geaz/muRLi/circuit/kicad/MOD.sch

## KiCad design circuit/kicad/MOD.sch (2020-06-06)

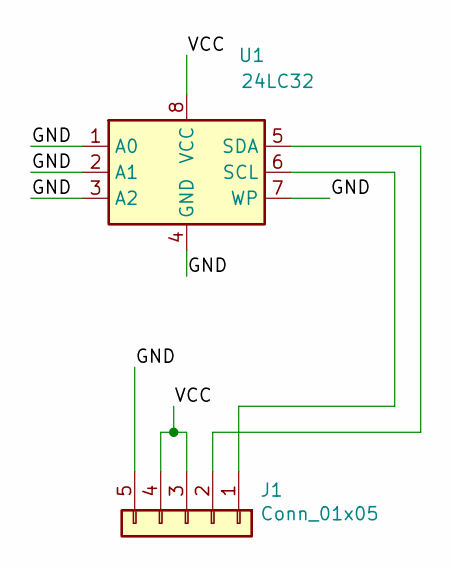
[picture p32: schematic MOD.sch]

Parts:
J1: Conn_01x05
U1: 24LC32

Connections:
GND: J1.5, U1.1 (A0), U1.2 (A1), U1.3 (A2), U1.4 (GND), U1.7 (WP)
unnamed: J1.1, U1.6 (SCL)
unnamed: J1.2, U1.5 (SDA)
VCC: J1.3, J1.4, U1.8 (VCC)
