geaz/muRLi/src/firmware/src/murli/states/invalid_mod_state.cpp

#ifndef INVALIDMODSTATE_H
#define INVALIDMODSTATE_H

#include "../state.hpp"
#include "../murli_context.hpp"
#include "../../views/icon_text_view.cpp"

namespace Murli
{
    class InvalidModState : public State
    {
        public:
            InvalidModState()
            {
                _invalidModView = std::make_shared<IconTextView>("Invalid MOD ...", u8g2_font_open_iconic_check_2x_t, 66);
            }

            void run(MurliContext& context)
            {
                context.getLed().setAllLeds(Murli::Red);
                context.getDisplay().setView(_invalidModView);
            }

        private:
            std::shared_ptr<IconTextView> _invalidModView;
    };
}

#endif // INVALIDMODSTATE_H
