geaz/muRLi/src/firmware/src/network/websocket/socket_server.cpp

#include "socket_server.hpp"

namespace Murli
{
    SocketServer::SocketServer()
    {
        _webSocket.begin();
        _webSocket.onEvent([this](uint8_t num, WStype_t type, uint8_t * payload, size_t length){ serverEvent(num, type, payload, length); });
    }

    void SocketServer::loop()
    {
        _webSocket.loop();
    }

    void SocketServer::broadcast(Client::Command command)
    {
        // Only MESH_COUNT_REQUEST and MESH_UPDATE are awaiting answers
        if (command.commandType == Client::MESH_COUNT_REQUEST
        || command.commandType == Client::MESH_UPDATE)
        {
            _answers = 0;
            _requestCommand = command;
        }

        size_t commandSize = sizeof(command);
        uint8_t serializedCommand[commandSize];
        memcpy(&serializedCommand, &command, commandSize);

        _webSocket.broadcastBIN(&serializedCommand[0], commandSize);
    }

    void SocketServer::broadcastMod(std::string& mod)
    {
        _answers = 0;
        _modDistribution = true;
        _webSocket.broadcastTXT(mod.c_str(), mod.length());
    }

    uint32_t SocketServer::getClientsCount()
    {
        return _webSocket.connectedClients();
    }

    void SocketServer::serverEvent(uint8_t num, WStype_t type, uint8_t * payload, size_t length)
    {
        IPAddress remoteIp = _webSocket.remoteIP(num);
        switch(type) 
        {
            case WStype_DISCONNECTED:              
                Serial.println("Client disconnected!");
                for(auto event : meshConnectionEvents.getEventHandlers()) event.second();
                break;
            case WStype_CONNECTED:        
                Serial.println("Connection from: " + remoteIp.toString());
                for(auto event : meshConnectionEvents.getEventHandlers()) event.second();
                break;
            case WStype_BIN:
                Server::Command receivedCommand;
                memcpy(&receivedCommand, payload, length);
                if(allAnswerReceived(receivedCommand))
                {
                    _requestCommand.id = 0;
                    _modDistribution = false;
                    for(auto event : serverCommandEvents.getEventHandlers()) event.second(_receivedCommand); 
                }
                break;
            default:
                break;
        }
    }

    bool SocketServer::allAnswerReceived(Server::Command receivedCommand)
    {
        bool allReceived = false;
        // We want to wait for the answers of all connected clients
        // EXTERNAL_ANALYZER and MESH_CONNECTION are not answer commands - thats why we exclude them here
        if(receivedCommand.commandType != Server::EXTERNAL_ANALYZER
        && receivedCommand.commandType != Server::MESH_CONNECTION)
        {            
            if(_requestCommand.id == receivedCommand.id || _modDistribution)
            {
                _answers++;
                if (_answers == 1
                || (receivedCommand.commandType == Server::MESH_COUNTED 
                && _receivedCommand.countedCommand.meshLedCount < receivedCommand.countedCommand.meshLedCount))
                {
                    _receivedCommand = receivedCommand;
                }
                allReceived = _answers == _webSocket.connectedClients();
            }
        }
        else
        {
            allReceived = true;
            _receivedCommand = receivedCommand;
        }
        return allReceived;
    }
}
